skalnik/PR_Public_Radio_Firmware/PR2001 Speaker Swan B3S.SLDPRT

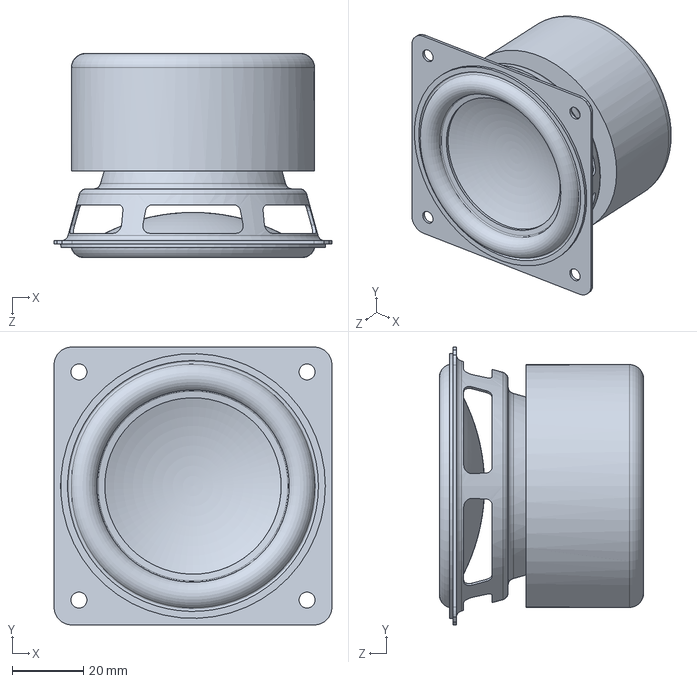
[picture p13: CAD file, 2013-09-14, last stored version]
PR2001 Speaker Swan B3S.SLDPRT
78.0 x 78.0 x 57.3 mm
