skalnik/PR_Public_Radio_Firmware/PR_Solidworks/PR2005 Potentiometer Bourns BTR901-2015K-A103.SLDPRT

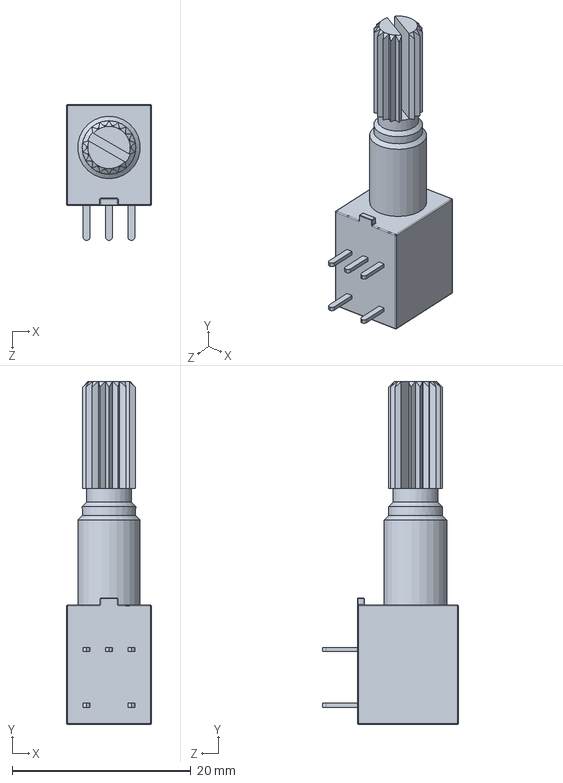
[picture p14: CAD file, 2013-09-14, last stored version]
PR_Solidworks/PR2005 Potentiometer Bourns BTR901-2015K-A103.SLDPRT
9.50 x 38.4 x 15.2 mm
