skalnik/PR_Public_Radio_Firmware/PR1004 Fibonacci Lid.SLDPRT

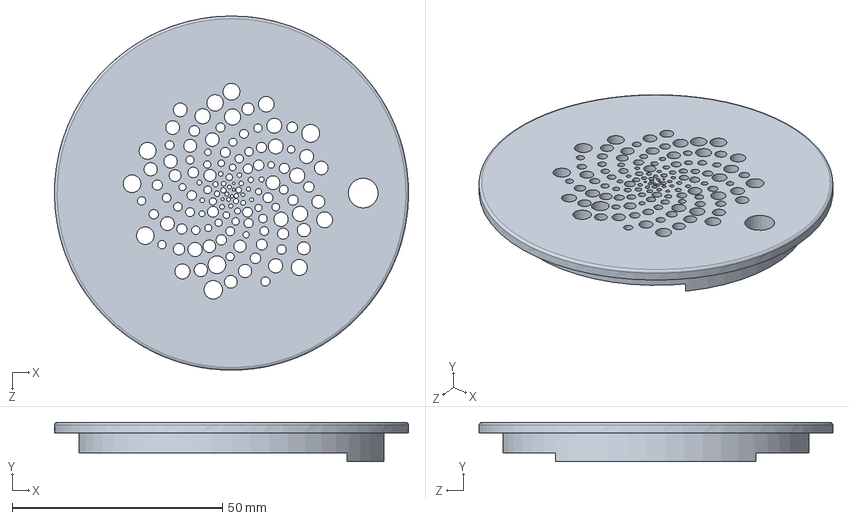
[picture p15: CAD file, 2013-09-14, last stored version]
PR1004 Fibonacci Lid.SLDPRT
84.3 x 9.30 x 84.3 mm
